charles-waite/WALL-Env-idf/main/drivers/OLEDDisplayFonts.h

#ifndef OLEDDISPLAYFONTS_h
#define OLEDDISPLAYFONTS_h

#ifndef PROGMEM
#define PROGMEM
#endif

#ifdef __MBED__
#define PROGMEM
#endif

const uint8_t ArialMT_Plain_10[] PROGMEM = {
  0x0A, // Width: 10
  0x0D, // Height: 13
  0x20, // First Char: 32
  0xE0, // Numbers of Chars: 224

  // Jump Table:
  0xFF, 0xFF, 0x00, 0x03,  // 32:65535
  0x00, 0x00, 0x04, 0x03,  // 33:0
  0x00, 0x04, 0x05, 0x04,  // 34:4
  0x00, 0x09, 0x09, 0x06,  // 35:9
  0x00, 0x12, 0x0A, 0x06,  // 36:18
  0x00, 0x1C, 0x10, 0x09,  // 37:28
  0x00, 0x2C, 0x0E, 0x07,  // 38:44
  0x00, 0x3A, 0x01, 0x02,  // 39:58
  0x00, 0x3B, 0x06, 0x03,  // 40:59
  0x00, 0x41, 0x06, 0x03,  // 41:65
  0x00, 0x47, 0x05, 0x04,  // 42:71
  0x00, 0x4C, 0x09, 0x06,  // 43:76
  0x00, 0x55, 0x04, 0x03,  // 44:85
  0x00, 0x59, 0x03, 0x03,  // 45:89
  0x00, 0x5C, 0x04, 0x03,  // 46:92
  0x00, 0x60, 0x05, 0x03,  // 47:96
  0x00, 0x65, 0x0A, 0x06,  // 48:101
  0x00, 0x6F, 0x08, 0x06,  // 49:111
  0x00, 0x77, 0x0A, 0x06,  // 50:119
  0x00, 0x81, 0x0A, 0x06,  // 51:129
  0x00, 0x8B, 0x0B, 0x06,  // 52:139
  0x00, 0x96, 0x0A, 0x06,  // 53:150
  0x00, 0xA0, 0x0A, 0x06,  // 54:160
  0x00, 0xAA, 0x09, 0x06,  // 55:170
  0x00, 0xB3, 0x0A, 0x06,  // 56:179
  0x00, 0xBD, 0x0A, 0x06,  // 57:189
  0x00, 0xC7, 0x04, 0x03,  // 58:199
  0x00, 0xCB, 0x04, 0x03,  // 59:203
  0x00, 0xCF, 0x0A, 0x06,  // 60:207
  0x00, 0xD9, 0x09, 0x06,  // 61:217
  0x00, 0xE2, 0x09, 0x06,  // 62:226
  0x00, 0xEB, 0x0B, 0x06,  // 63:235
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
  0x00,0x00,0x00,0x00,0x00,0x00,0x00,0x00,0xE0,0xFF,0x3F,0x00,0xE0,0xFF,0x3F,0x00,0x60,0x30,0x00,0x00,0x60,0x30,0x00,0x00,0x60,0x30,0x00,0x00,0x60,0x30,0x00,0x00,0x60,0x30,0x00,0x00,0x60,0x30,0x00,0x00,0x60,0x30,0x00,0x00,0x60,0x30,0x00,0x00,0x60,0x30,0x00,0x00,0x60, // 70
  0x00,0x00,0x00,0x00,0x00,0xFC,0x01,0x00,0x00,0xFF,0x07,0x00,0x80,0x07,0x0F,0x00,0xC0,0x01,0x1C,0x00,0xC0,0x00,0x18,0x00,0xE0,0x00,0x18,0x00,0x60,0x00,0x30,0x00,0x60,0x00,0x30,0x00,0x60,0x00,0x30,0x00,0x60,0x60,0x30,0x00,0x60,0x60,0x30,0x00,0xE0,0x60,0x38,0x00,0xC0,0x60,0x18,0x00,0xC0,0x61,0x18,0x00,0x80,0xE3,0x0F,0x00,0x00,0xE2,0x0F, // 71
  0x00,0x00,0x00,0x00,0x00,0x00,0x00,0x00,0xE0,0xFF,0x3F,0x00,0xE0,0xFF,0x3F,0x00,0x00,0x30,0x00,0x00,0x00,0x30,0x00,0x00,0x00,0x30,0x00,0x00,0x00,0x30,0x00,0x00,0x00,0x30,0x00,0x00,0x00,0x30,0x00,0x00,0x00,0x30,0x00,0x00,0x00,0x30,0x00,0x00,0x00,0x30,0x00,0x00,0xE0,0xFF,0x3F,0x00,0xE0,0xFF,0x3F, // 72
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
};
#endif
