charles-waite/WALL-Env-idf/main/drivers/kirby.h

#pragma once

static constexpr int KIRBY_W = 64;
static constexpr int KIRBY_H = 64;

static const unsigned char kirby_bits[] = { // Kirby 64x64
  0x00, 0x00, 0x00, 0x00, 0x00, 0x00, 0x00, 0x00, 0x00, 0x00, 0x00, 0x00,
  0x00, 0x00, 0x00, 0x00, 0x00, 0x00, 0x00, 0x00, 0x00, 0x00, 0x00, 0x00,
  0x00, 0x00, 0x00, 0x00, 0x00, 0x00, 0x00, 0x00, 0x00, 0x00, 0x00, 0xFC,
  0x1F, 0x00, 0x00, 0x00, 0x00, 0x00, 0x80, 0xFF, 0xFF, 0x00, 0x00, 0x00,
  0x00, 0x00, 0xE0, 0x03, 0xC0, 0x03, 0x00, 0x00, 0x00, 0x00, 0x78, 0x00,
  0x00, 0x0F, 0x00, 0x00, 0x00, 0x00, 0x1C, 0x00, 0x00, 0x1C, 0x00, 0x00,
  0x00, 0x00, 0x0E, 0x00, 0x00, 0x30, 0x00, 0x00, 0x00, 0x00, 0x03, 0x00,
  0x00, 0xE0, 0x00, 0x00, 0x00, 0x80, 0x01, 0x00, 0x00, 0xC0, 0x00, 0x00,
  0x00, 0xC0, 0x00, 0x0C, 0x18, 0x80, 0x01, 0x00, 0x00, 0x60, 0x00, 0x12,
  0x24, 0x00, 0x03, 0x00, 0x00, 0x70, 0x00, 0x10, 0x04, 0x00, 0x06, 0x00,
  0x00, 0x30, 0x00, 0x11, 0x44, 0x00, 0x06, 0x00, 0x00, 0x18, 0x00, 0x11,
  0x64, 0x00, 0x0C, 0x00, 0x00, 0x18, 0x00, 0x1B, 0x6C, 0x00, 0x0C, 0x00,
  0x00, 0x0C, 0x00, 0x1F, 0x7C, 0x00, 0x18, 0x00, 0x00, 0x0C, 0x00, 0x1F,
  0x7C, 0x00, 0x18, 0x00, 0x00, 0x0C, 0x00, 0x1F, 0x7C, 0x00, 0x10, 0x00,
  0x00, 0x04, 0x00, 0x1F, 0x7C, 0x00, 0x30, 0x00, 0x00, 0x07, 0x00, 0x1F,
  0x3C, 0x00, 0xF0, 0x00, 0xC0, 0x07, 0x1E, 0x0E, 0x38, 0x3C, 0xE0, 0x03,
  0xE0, 0x00, 0x3F, 0x0E, 0x38, 0x7E, 0x00, 0x07, 0x30, 0x00, 0x3F, 0x00,
  0x00, 0x7E, 0x00, 0x0C, 0x18, 0x00, 0x0E, 0xE0, 0x03, 0x3C, 0x00, 0x18,
  0x0C, 0x00, 0x00, 0xF0, 0x07, 0x00, 0x00, 0x30, 0x0C, 0x00, 0x00, 0x10,
  0x04, 0x00, 0x00, 0x30, 0x04, 0x00, 0x00, 0x00, 0x00, 0x00, 0x00, 0x20,
  0x06, 0x00, 0x00, 0x20, 0x02, 0x00, 0x00, 0x60, 0x06, 0x00, 0x00, 0xC0,
  0x01, 0x00, 0x00, 0x60, 0x06, 0x00, 0x00, 0x00, 0x00, 0x00, 0x00, 0x20,
  0x0C, 0x00, 0x00, 0x00, 0x00, 0x00, 0x00, 0x30, 0x0C, 0x00, 0x00, 0x00,
  0x00, 0x00, 0x00, 0x30, 0x18, 0x00, 0x00, 0x00, 0x00, 0x00, 0x00, 0x18,
  0x38, 0x00, 0x00, 0x00, 0x00, 0x00, 0x00, 0x1C, 0xF0, 0x31, 0x00, 0x00,
  0x00, 0x00, 0x8E, 0x07, 0xC0, 0x7F, 0x00, 0x00, 0x00, 0x00, 0xFE, 0x03,
  0x00, 0x60, 0x00, 0x00, 0x00, 0x00, 0x03, 0x00, 0x00, 0xF8, 0x00, 0x00,
  0x00, 0x80, 0x0F, 0x00, 0x00, 0x9C, 0x01, 0x00, 0x00, 0xC0, 0x1C, 0x00,
  0x00, 0x06, 0x03, 0x00, 0x00, 0xE0, 0x30, 0x00, 0x00, 0x03, 0x0E, 0x00,
  0x00, 0x30, 0x60, 0x00, 0x80, 0x01, 0x1C, 0x00, 0x00, 0x1C, 0xC0, 0x00,
  0xC0, 0x00, 0x78, 0x00, 0x00, 0x0F, 0x80, 0x01, 0xC0, 0x00, 0xE0, 0x03,
  0xC0, 0x03, 0x80, 0x01, 0x60, 0x00, 0x80, 0xFF, 0xFF, 0x00, 0x00, 0x03,
  0x60, 0x00, 0x00, 0xF8, 0x1F, 0x00, 0x00, 0x03, 0x60, 0x00, 0x00, 0x30,
  0x06, 0x00, 0x00, 0x03, 0x60, 0x00, 0x00, 0x18, 0x0C, 0x00, 0x00, 0x03,
  0x60, 0x00, 0x00, 0x1C, 0x1C, 0x00, 0x00, 0x03, 0xC0, 0x00, 0x00, 0x0E,
  0x38, 0x00, 0x80, 0x01, 0xC0, 0x00, 0x00, 0x07, 0x70, 0x00, 0x80, 0x01,
  0x80, 0x03, 0xC0, 0x01, 0xC0, 0x01, 0xE0, 0x00, 0x00, 0x0F, 0xF8, 0x00,
  0x80, 0x0F, 0x78, 0x00, 0x00, 0xFC, 0x3F, 0x00, 0x00, 0xFE, 0x1F, 0x00,
  0x00, 0xE0, 0x03, 0x00, 0x00, 0xE0, 0x03, 0x00, 0x00, 0x00, 0x00, 0x00,
  0x00, 0x00, 0x00, 0x00, 0x00, 0x00, 0x00, 0x00, 0x00, 0x00, 0x00, 0x00,
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
};
