charles-waite/WALL-Env-idf/main/drivers/shtc3.cpp

/*
   This example code is in the Public Domain (or CC0 licensed, at your option.)

   Unless required by applicable law or agreed to in writing, this
   software is distributed on an "AS IS" BASIS, WITHOUT WARRANTIES OR
   CONDITIONS OF ANY KIND, either express or implied.
*/

#include <esp_err.h>
#include <esp_log.h>
#include <esp_timer.h>
#include <esp_random.h>
#include <driver/i2c_master.h>

#include <lib/support/CodeUtils.h>

#include <drivers/i2c_bus.h>
#include <drivers/shtc3.h>

static const char * TAG = "shtc3";

#define SHTC3_SENSOR_ADDR 0x70      /*!< I2C address of SHTC3 sensor */

typedef struct {
    shtc3_sensor_config_t *config;
    esp_timer_handle_t timer;
    bool is_initialized = false;
} shtc3_sensor_ctx_t;

static shtc3_sensor_ctx_t s_ctx;
static i2c_master_dev_handle_t s_dev;

static esp_err_t shtc3_init_i2c()
{
    return i2c_bus_add_device(SHTC3_SENSOR_ADDR, &s_dev);
}

static esp_err_t shtc3_read(uint8_t *data, size_t size)
{
    const uint8_t cmd[] = {0x7C, 0xA2}; // temp + humidity, clock stretching
    esp_err_t err = i2c_master_transmit(s_dev, cmd, sizeof(cmd), 1000);
    if (err != ESP_OK) {
        return err;
    }

    // Wait for measurement to complete
    vTaskDelay(pdMS_TO_TICKS(15));

    return i2c_master_receive(s_dev, data, size, 1000);
}

// Temperature in degree Celsius
static float shtc3_get_temp(uint16_t raw_temp)
{
    return 175.0f * (static_cast<float>(raw_temp) / 65535.0f) - 45.0f;
}

// Humidity in percentage
static float shtc3_get_humidity(uint16_t raw_humidity)
{
    return 100.0f * (static_cast<float>(raw_humidity) / 65535.0f);
}

static esp_err_t shtc3_get_read_temp_and_humidity(float  &temp, float  &humidity)
{
    // foreach temperature and humidity: two bytes data, one byte for checksum
    uint8_t data[6] = {0};

    esp_err_t err = shtc3_read(data, sizeof(data));
    if (err != ESP_OK) {
        return err;
    }

    uint16_t raw_temp = (data[0] << 8) | data[1];
    uint16_t raw_humidity = (data[3] << 8) | data[4];

    temp = shtc3_get_temp(raw_temp);
    humidity = shtc3_get_humidity(raw_humidity);

    return ESP_OK;
}

static void timer_cb_internal(void *arg)
{
    auto *ctx = (shtc3_sensor_ctx_t *) arg;
    if (!(ctx && ctx->config)) {
        return;
    }

    float temp, humidity;
    esp_err_t err = shtc3_get_read_temp_and_humidity(temp, humidity);
    if (err != ESP_OK) {
        return;
    }
    if (ctx->config->temperature.cb) {
        ctx->config->temperature.cb(ctx->config->temperature.endpoint_id, temp, ctx->config->user_data);
    }
    if (ctx->config->humidity.cb) {
        ctx->config->humidity.cb(ctx->config->humidity.endpoint_id, humidity, ctx->config->user_data);
    }
}

esp_err_t shtc3_sensor_init(shtc3_sensor_config_t *config)
{
    if (config == NULL) {
        return ESP_ERR_INVALID_ARG;
    }
    // we need at least one callback so that we can start notifying application layer
    if (config->temperature.cb == NULL || config->humidity.cb == NULL) {
        return ESP_ERR_INVALID_ARG;
    }
    if (s_ctx.is_initialized) {
        return ESP_ERR_INVALID_STATE;
    }

    esp_err_t err = shtc3_init_i2c();
    if (err != ESP_OK) {
        return err;
    }

    // keep the pointer to config
    s_ctx.config = config;

    esp_timer_create_args_t args = {
        .callback = timer_cb_internal,
        .arg = &s_ctx,
    };

    err = esp_timer_create(&args, &s_ctx.timer);
    if (err != ESP_OK) {
        ESP_LOGE(TAG, "esp_timer_create failed, err:%d", err);
        return err;
    }

    err = esp_timer_start_periodic(s_ctx.timer, config->interval_ms * 1000);
    if (err != ESP_OK) {
        ESP_LOGE(TAG, "esp_timer_start_periodic failed: %d", err);
        return err;
    }

    s_ctx.is_initialized = true;
    ESP_LOGI(TAG, "shtc3 initialized successfully");

    return ESP_OK;
}
